ingelectronicadj/IoT-para-medir-peso-al-interior-de-un-contendeor/RegresionLog/datos_1k.png

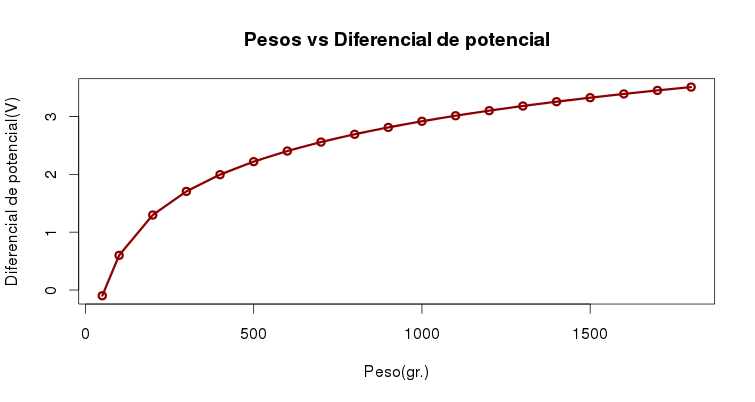
RegresionLog/datos_1k.png
