ingelectronicadj/IoT-para-medir-peso-al-interior-de-un-contendeor/LecturaADC_FSR.ino

//Lectura ADC del FSR
int FSR_Pin = A0; //analog pin 0

void setup(){
  Serial.begin(9600);
}

void loop(){
  int FSRReading = analogRead(FSR_Pin); 

  Serial.println(FSRReading);
  delay(250); //just here to slow down the output for easier reading
}
